Val01-x/EOS_2024/Documentation/Entonnoir/WhatsApp Image 2024-02-01 at 12.17.04.jpeg

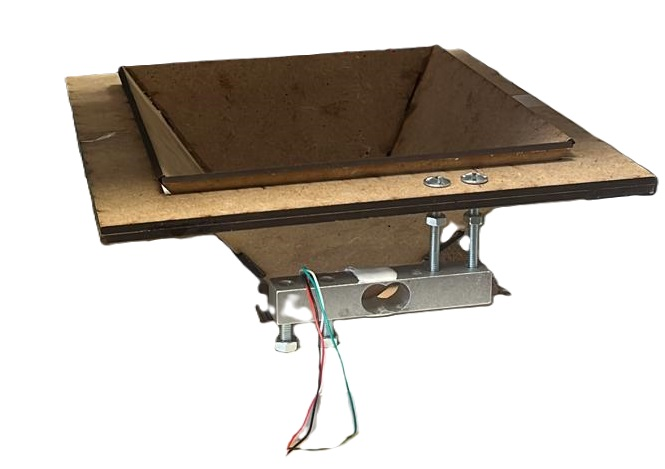
Documentation/Entonnoir/WhatsApp Image 2024-02-01 at 12.17.04.jpeg
