Val01-x/EOS_2024/Documentation/EOS complet/WhatsApp Image 2024-02-01 at 12.16.42.jpeg

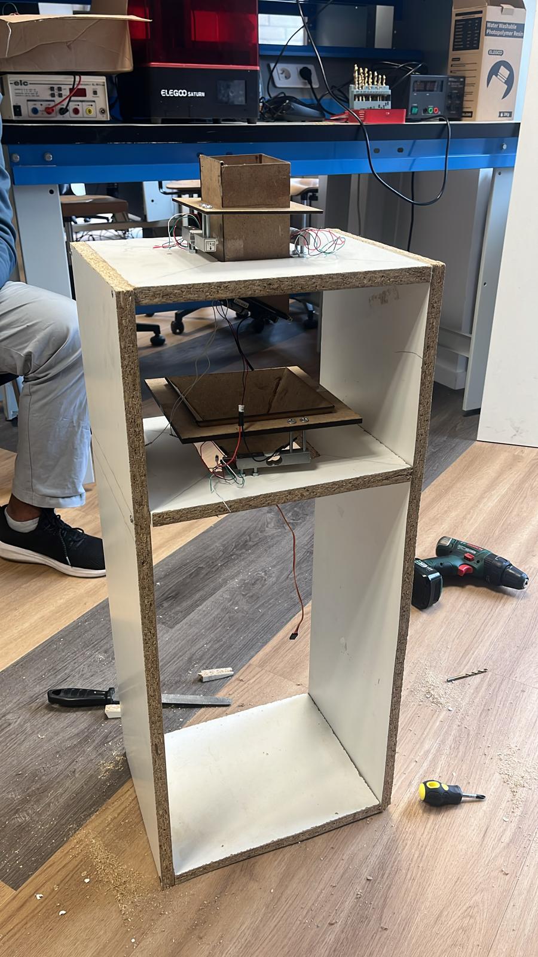
Documentation/EOS complet/WhatsApp Image 2024-02-01 at 12.16.42.jpeg
