Val01-x/EOS_2024/Module sertissage/Composants/BreadBoard.png

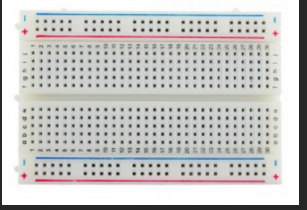
Module sertissage/Composants/BreadBoard.png
