Val01-x/EOS_2024/Module sertissage/Composants/Fil de nichrone.png

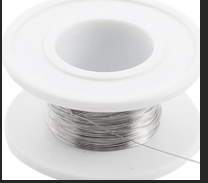
Module sertissage/Composants/Fil de nichrone.png
