Val01-x/EOS_2024/Module sertissage/Composants/Planche De Bois.png

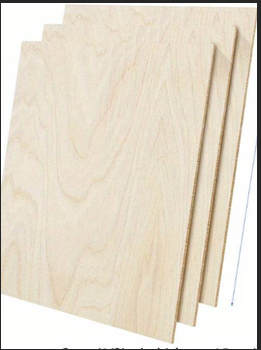
Module sertissage/Composants/Planche De Bois.png
