Val01-x/EOS_2024/Module sertissage/Electronique/BranchementCert.png

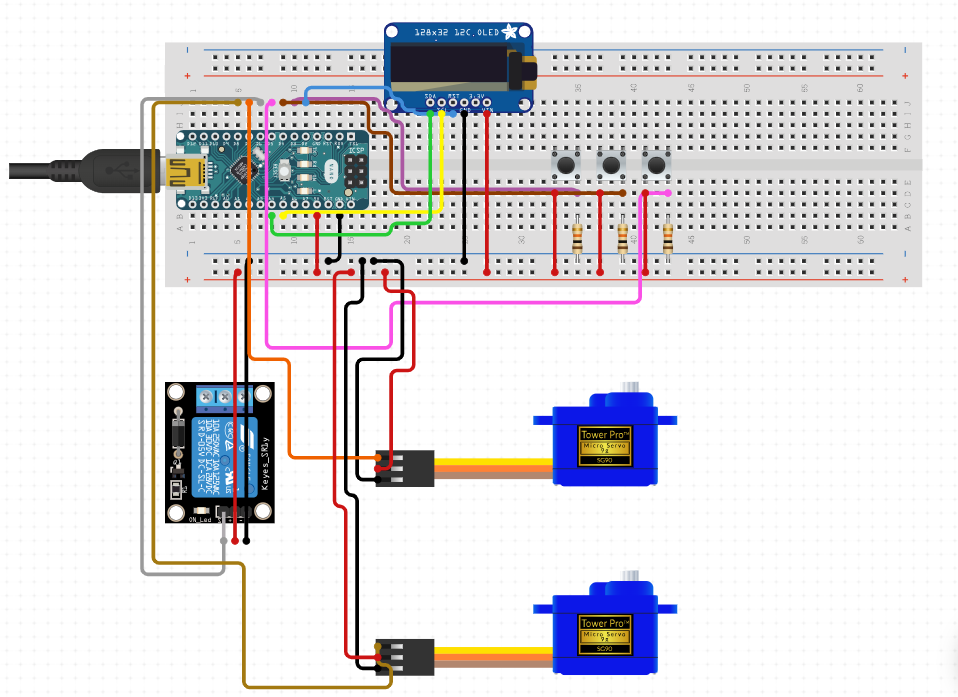
Module sertissage/Electronique/BranchementCert.png
