Val01-x/EOS_2024/module versement/Composant/ArduinoNano.png

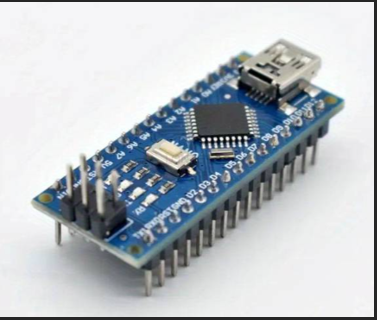
module versement/Composant/ArduinoNano.png
