Val01-x/EOS_2024/module versement/Composant/Cellule de charge + Module Hx711.png

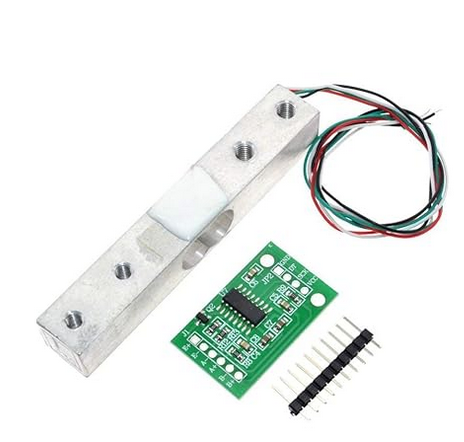
module versement/Composant/Cellule de charge + Module Hx711.png
