Val01-x/EOS_2024/module versement/Composant/servo.png

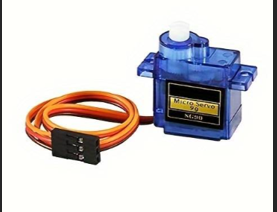
module versement/Composant/servo.png
