Val01-x/EOS_2024/module versement/Electronique/Branchement module versement.png

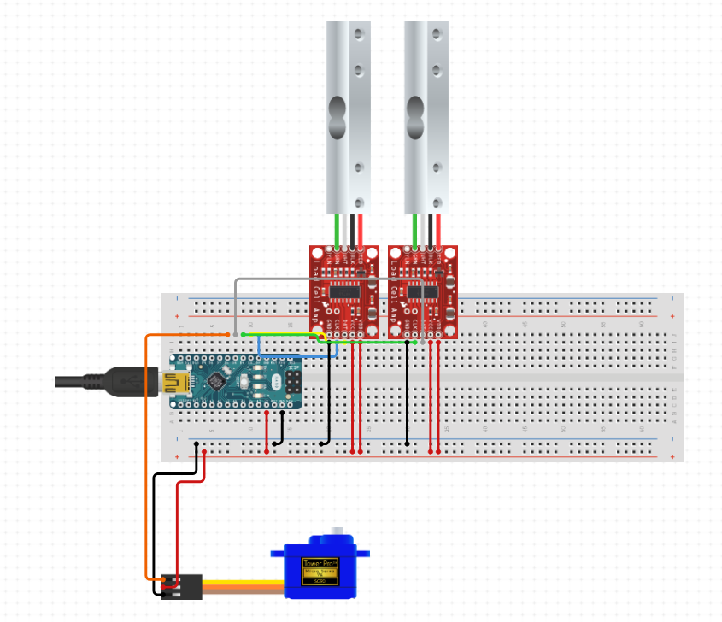
module versement/Electronique/Branchement module versement.png
